craftit/ForceSensingMantisGripper/src/ROS/mantis_gripper/meshes/visual/Mount_B.stl

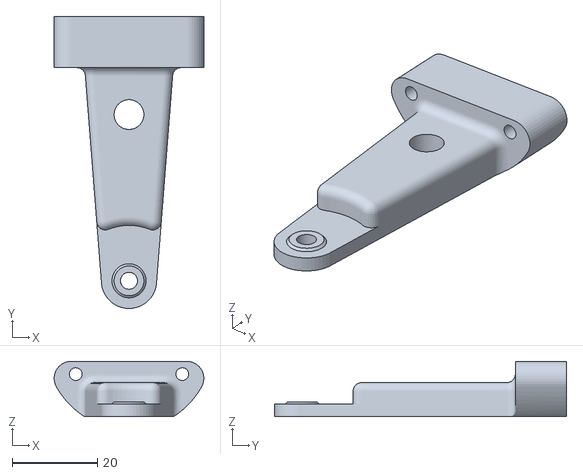
[picture p18: CAD file, 2017-01-06]
src/ROS/mantis_gripper/meshes/visual/Mount_B.stl
35.1 x 68.5 x 13.0
