craftit/ForceSensingMantisGripper/media/20170106_142106.jpg

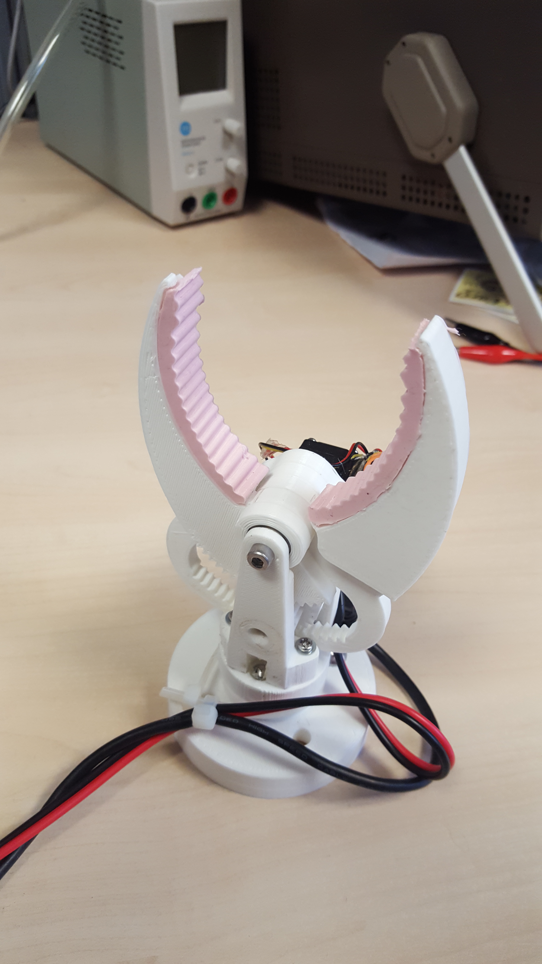
media/20170106_142106.jpg
